deyrudra/SmarterVenting/docs/3 - System/MQTT/writtenbrainstorm/image2.jpg

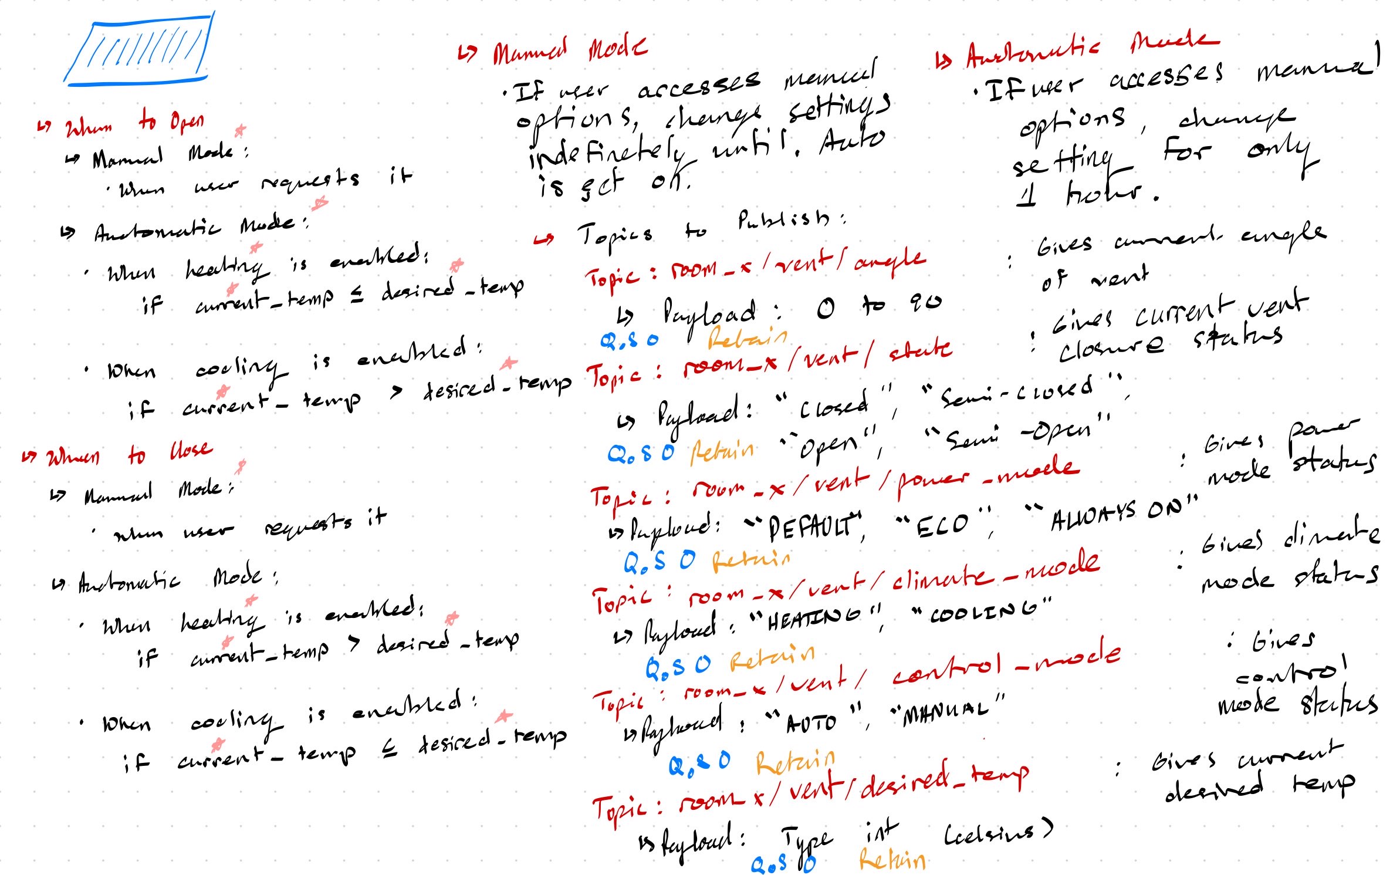
docs/3 - System/MQTT/writtenbrainstorm/image2.jpg
