deyrudra/SmarterVenting/docs/3 - System/MQTT/writtenbrainstorm/image3.jpg

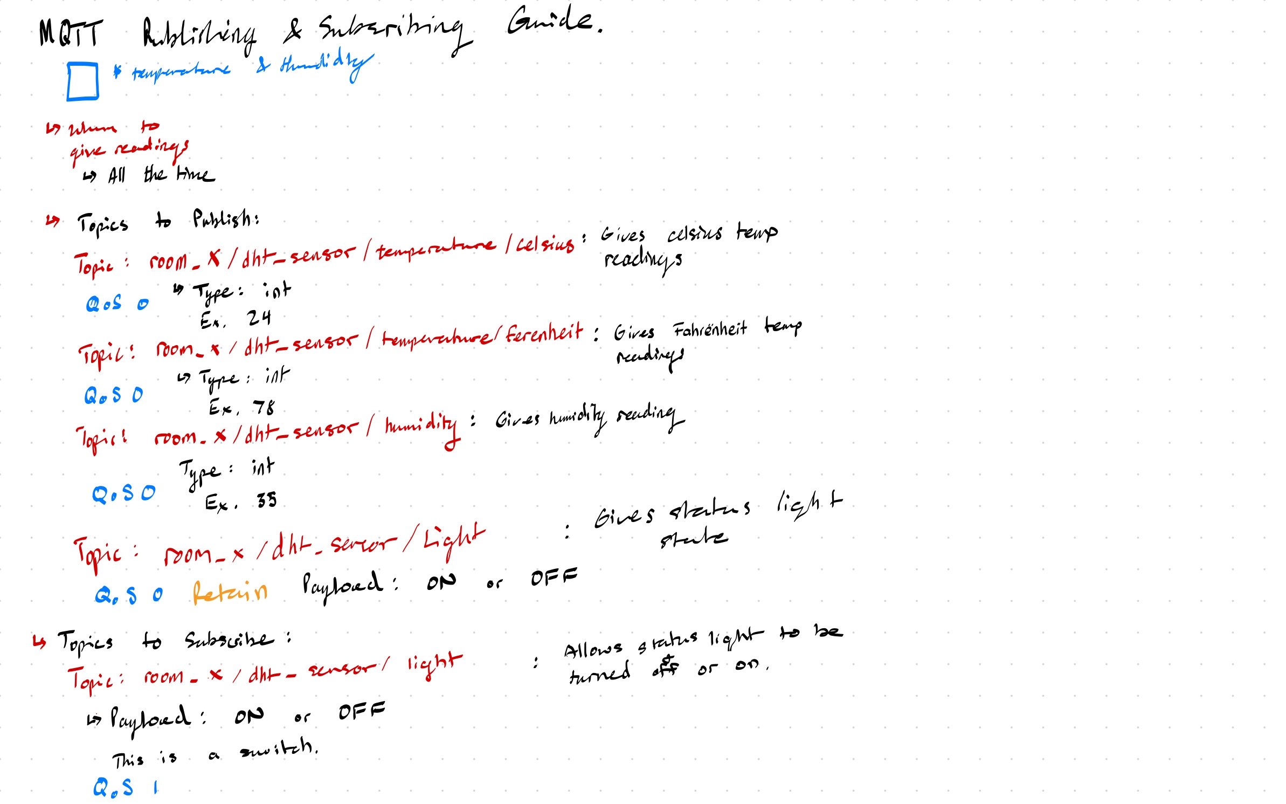
docs/3 - System/MQTT/writtenbrainstorm/image3.jpg
