deyrudra/SmarterVenting/models/Register1 (4x10, 3.54x9.61)/Fins/Fin 2 (16 cm).stl

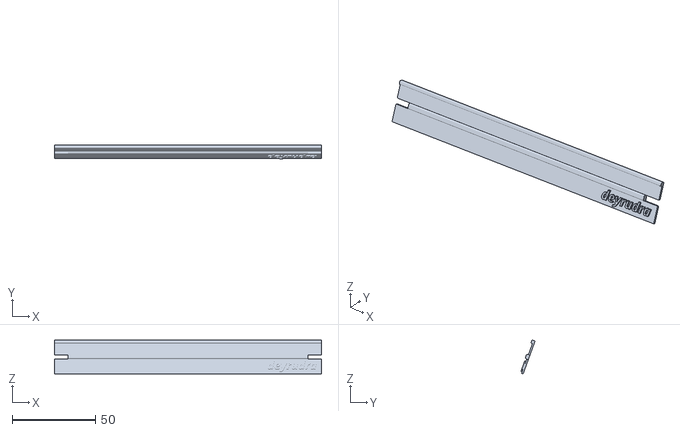
[picture p18: CAD file, 2024-08-21]
models/Register1 (4x10, 3.54x9.61)/Fins/Fin 2 (16 cm).stl
160.0 x 8.59 x 20.3
