deyrudra/SmarterVenting/models/Register1 (4x10, 3.54x9.61)/Mount and Mount Headers/Left Mount.stl

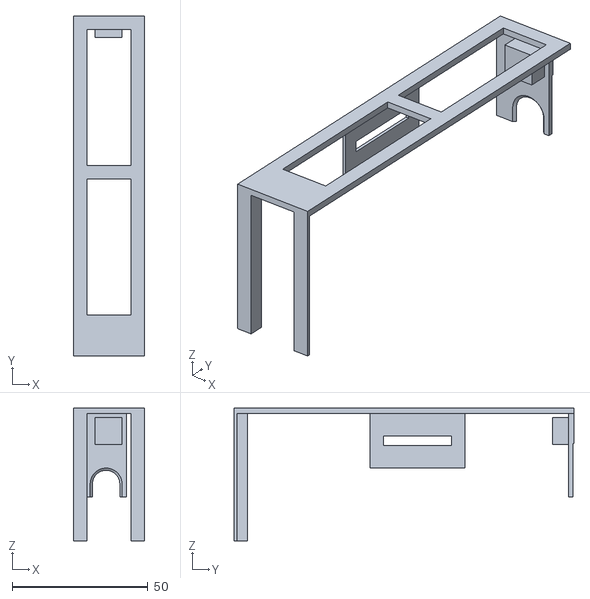
[picture p19: CAD file, 2024-08-21]
models/Register1 (4x10, 3.54x9.61)/Mount and Mount Headers/Left Mount.stl
26.0 x 125.0 x 48.9
