deyrudra/SmarterVenting/models/Register1 (4x10, 3.54x9.61)/Fins/Fin 1 (9.4 cm).stl

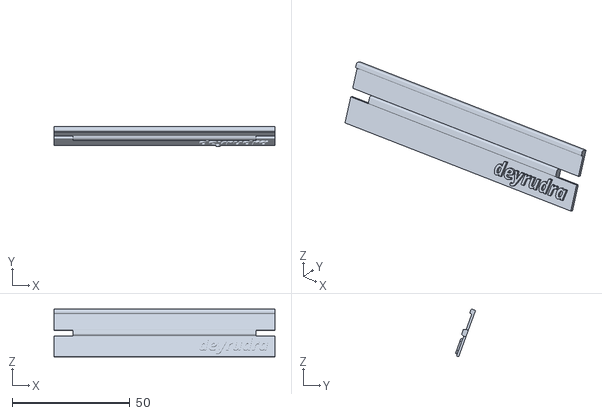
[picture p20: CAD file, 2024-08-21]
models/Register1 (4x10, 3.54x9.61)/Fins/Fin 1 (9.4 cm).stl
94.0 x 8.59 x 20.3
