deyrudra/SmarterVenting/models/Register1 (4x10, 3.54x9.61)/Mount and Mount Headers/Mount Header 2.stl

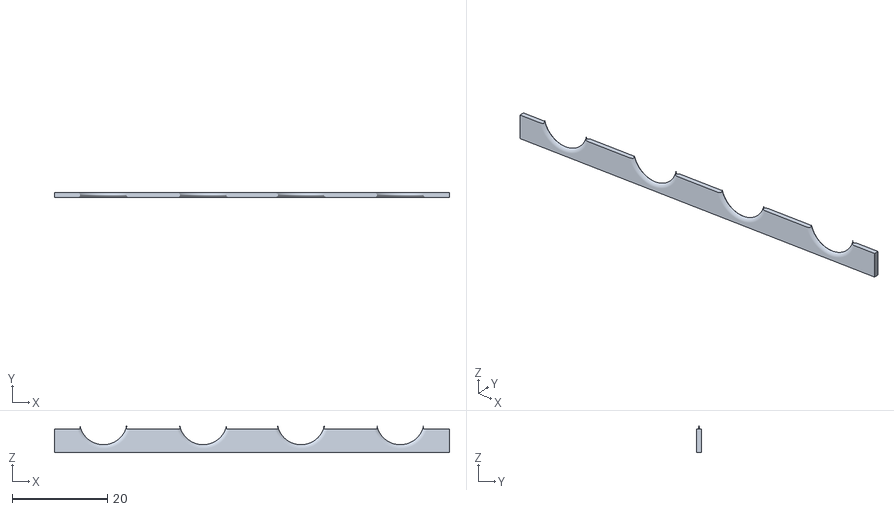
[picture p21: CAD file, 2024-08-21]
models/Register1 (4x10, 3.54x9.61)/Mount and Mount Headers/Mount Header 2.stl
82.7 x 1.00 x 5.52
