deyrudra/SmarterVenting/models/Register1 (4x10, 3.54x9.61)/Mount and Mount Headers/Mount Header 1 (x3).stl

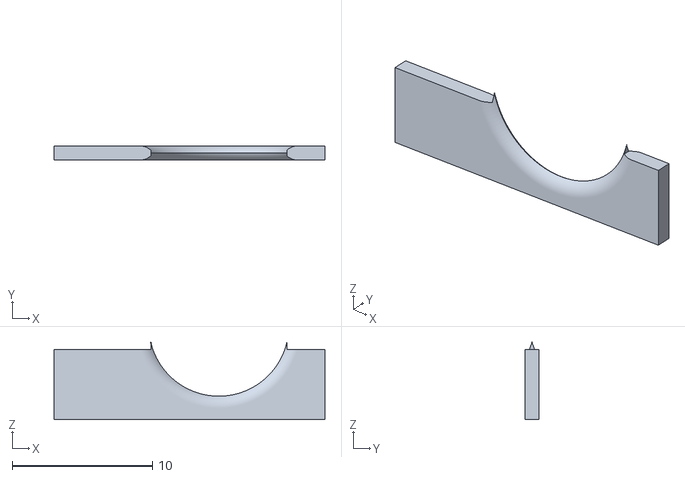
[picture p22: CAD file, 2024-08-21]
models/Register1 (4x10, 3.54x9.61)/Mount and Mount Headers/Mount Header 1 (x3).stl
19.4 x 1 x 5.52
