deyrudra/SmarterVenting/docs/testing/d1mini_mqtt_test_script.ino

// This script connects to the wifi automatically.

#include "secrets.h"

#include <ESP8266WiFi.h>
#include <PubSubClient.h>

WiFiClient espClient;
PubSubClient client(espClient);
unsigned long lastMsg = 0;
#define MSG_BUFFER_SIZE	(50)
char msg[MSG_BUFFER_SIZE];
int value = 0;

void connect_wifi() {
  // Wifi Connection
  WiFi.mode(WIFI_STA);
  WiFi.begin(WIFI_SSID, WIFI_PASS);

  Serial.print("Connecting to the wifi...");
  while (WiFi.status() != WL_CONNECTED){
    delay(500);
    Serial.print(".");
  }
  Serial.println();

  Serial.print("Connected, IP Address: ");
  Serial.println(WiFi.localIP());

}

void connect_mqtt_broker() {
  client.setServer(MQTT_BROKER_IP, MQTT_BROKER_PORT);
  client.setCallback(callback);
}

void callback(char* topic, byte* payload, unsigned int length) {
  Serial.print("Message arrived [");
  Serial.print(topic);
  Serial.print("] ");
  for (int i = 0; i < length; i++) {
    Serial.print((char)payload[i]);
  }
  Serial.println();

  // Switch on the LED if an 1 was received as first character
  if ((char)payload[0] == '1') {
    digitalWrite(BUILTIN_LED, LOW);   // Turn the LED on (Note that LOW is the voltage level
    // but actually the LED is on; this is because
    // it is active low on the ESP-01)
  } else {
    digitalWrite(BUILTIN_LED, HIGH);  // Turn the LED off by making the voltage HIGH
  }

}

void reconnect() {
  // Loop until we're reconnected
  while (!client.connected()) {
    Serial.print("Attempting MQTT connection...");
    // Create a random client ID
    String clientId = "temp_humidity_sensor_room_";
    clientId += String(random(0xffff), HEX);
    // Attempt to connect
    if (client.connect(clientId.c_str(), MQTT_USERNAME, MQTT_PASS)) {
      Serial.println("connected");
      // Once connected, publish an announcement...
      client.publish("thetopic", "1");
      // ... and resubscribe
      client.subscribe("thetopic", 1);
    } else {
      Serial.print("failed, rc=");
      Serial.print(client.state());
      Serial.println(" try again in 5 seconds");
      // Wait 5 seconds before retrying
      delay(5000);
    }
  }
}


void setup() {
  // Serial Connection
  Serial.begin(115200);
  Serial.println();

  // Built in LED indicator
  pinMode(BUILTIN_LED, OUTPUT);

  // Connect ESP8266 to wifi
  connect_wifi();

  // Connect to MQTT broker
  connect_mqtt_broker();
}
 

void loop() {

  if (!client.connected()) {
    reconnect();
  }
  client.loop();

  unsigned long now = millis();
  if (now - lastMsg > 2000) {
    lastMsg = now;
    ++value;
    snprintf (msg, MSG_BUFFER_SIZE, "hello world #%ld", value);
    Serial.print("Publish message: ");
    Serial.println(msg);
    client.publish("thetopic", "1");
  }
}
