deyrudra/SmarterVenting/docs/testing/secrets.h

#ifndef SECRETS_H
#define SECRETS_H

// Wi-Fi credentials
#define WIFI_SSID ""
#define WIFI_PASS ""

// MQTT Broker Information
#define MQTT_BROKER_IP ""
#define MQTT_BROKER_PORT 1883
#define MQTT_USERNAME ""
#define MQTT_PASS ""

#endif // SECRETS_H
